hockemk/RICOHFLEX-instaxback/photos/3-IMG_5429.jpg

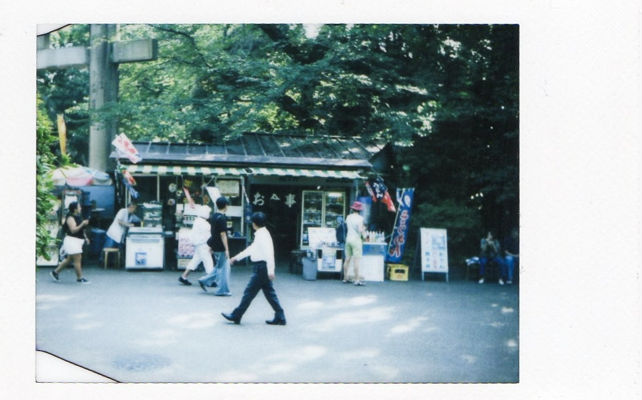
photos/3-IMG_5429.jpg
