hockemk/RICOHFLEX-instaxback/photos/5-IMG_5416.jpg

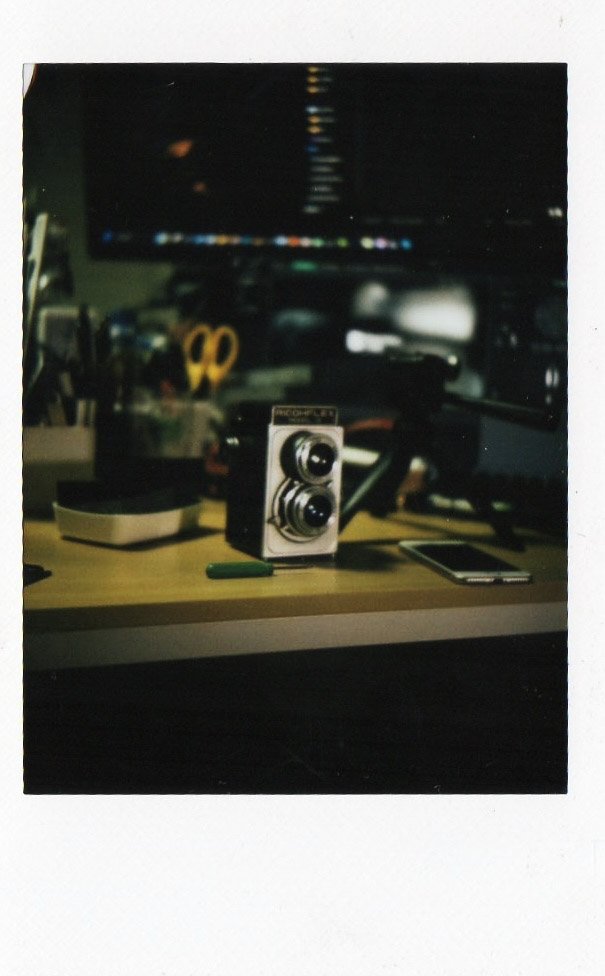
photos/5-IMG_5416.jpg
