hockemk/RICOHFLEX-instaxback/photos/6-IMG_5415.jpg

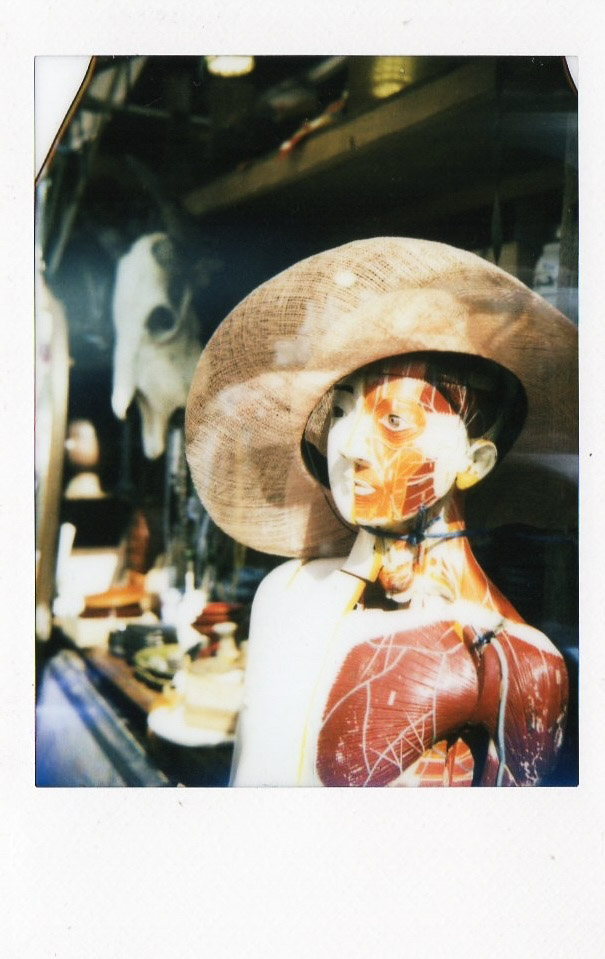
photos/6-IMG_5415.jpg
