hockemk/RICOHFLEX-instaxback/photos/9-IMG_5408.jpg

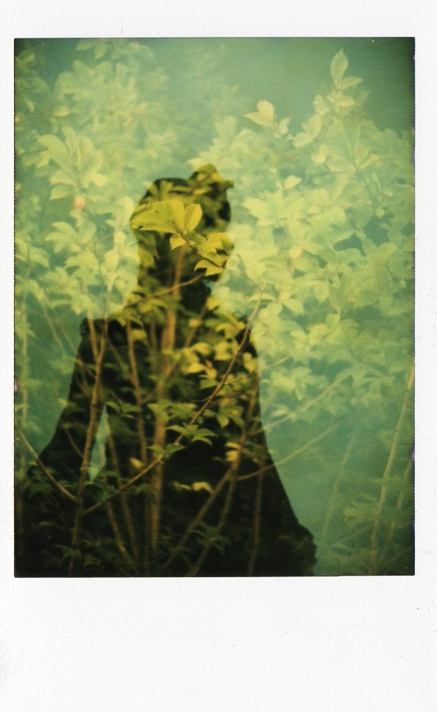
photos/9-IMG_5408.jpg
