hockemk/RICOHFLEX-instaxback/photos/IMG_5266.jpg

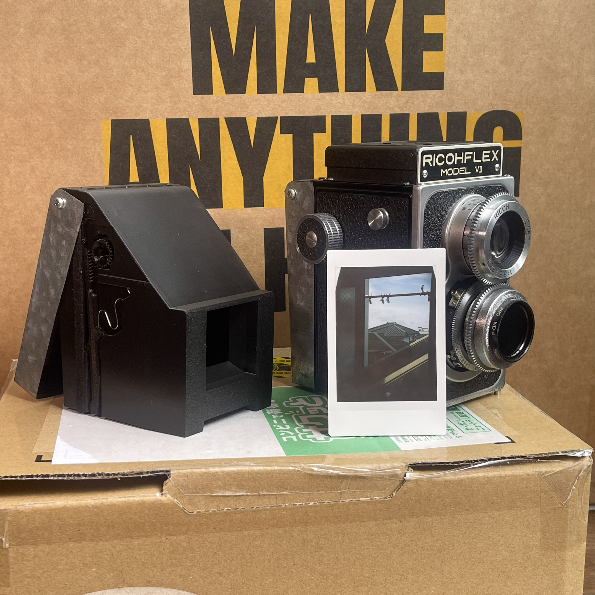
photos/IMG_5266.jpg
