hockemk/RICOHFLEX-instaxback/data/parts/P-09_RightRollerRetainer.step

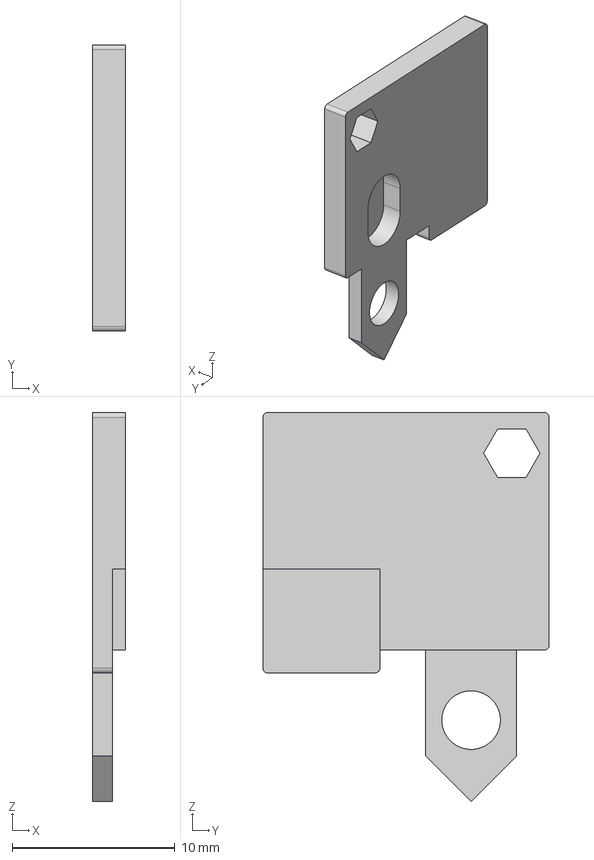
[picture p28: CAD file, 2026-07-20]
data/parts/P-09_RightRollerRetainer.step
2.00 x 17.6 x 23.9 mm
