hockemk/RICOHFLEX-instaxback/data/parts/P-12_RollerShaftCollar.step

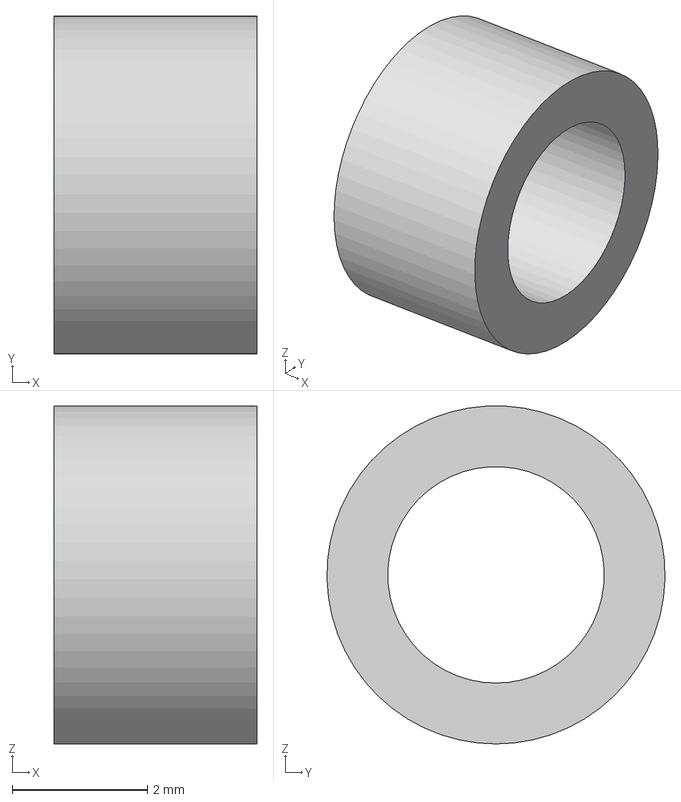
[picture p29: CAD file, 2026-07-20]
data/parts/P-12_RollerShaftCollar.step
3.00 x 5.00 x 5.00 mm
