hockemk/RICOHFLEX-instaxback/data/parts/M-11_BackPanel.step

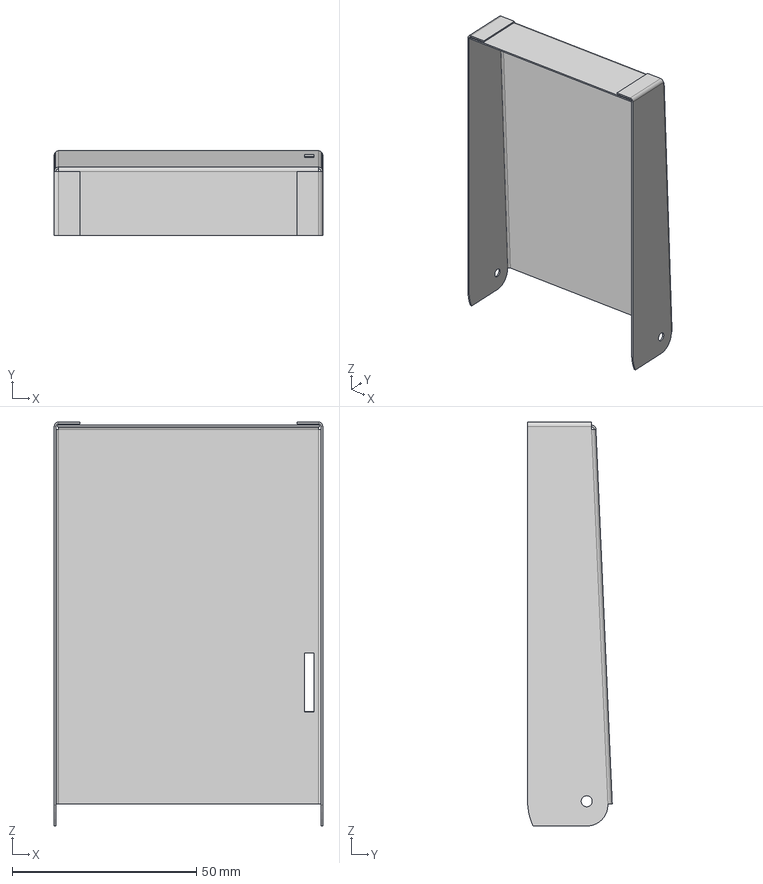
[picture p30: CAD file, 2026-07-20]
data/parts/M-11_BackPanel.step
72.8 x 22.9 x 109.5 mm
